waaraawa/Grow-Light/references/images/daiso_aluminum_cup_medium.png

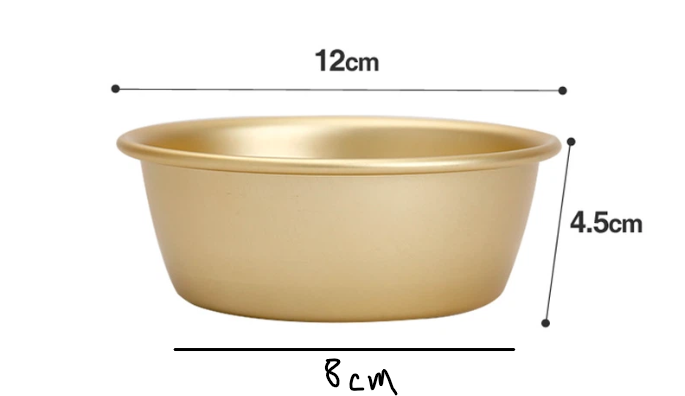
references/images/daiso_aluminum_cup_medium.png
