waaraawa/Grow-Light/references/images/usb_pd_trigger_board_low_voltage.png

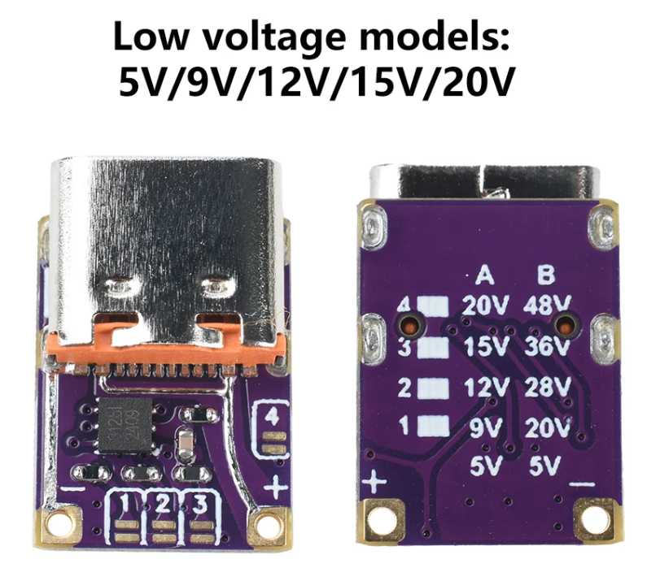
references/images/usb_pd_trigger_board_low_voltage.png
